slash128v6/DC34_Cnet_Badge/images/IMG_5186.JPEG

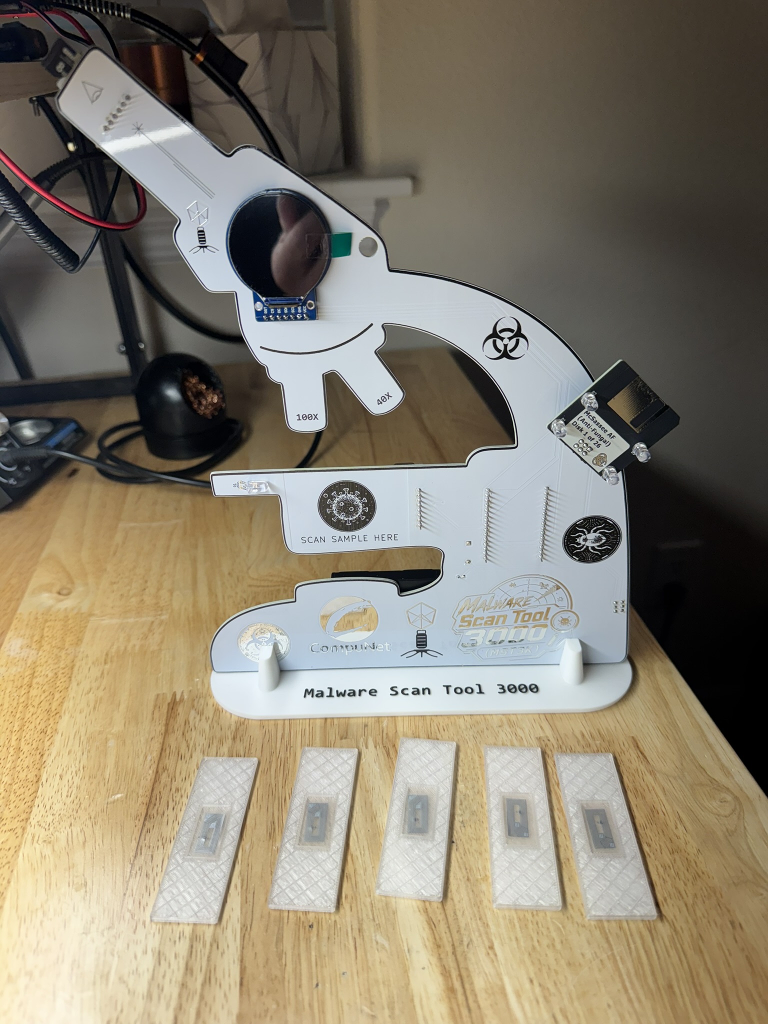
images/IMG_5186.JPEG
