slash128v6/DC34_Cnet_Badge/images/Screenshot 2026-06-05 122044.png

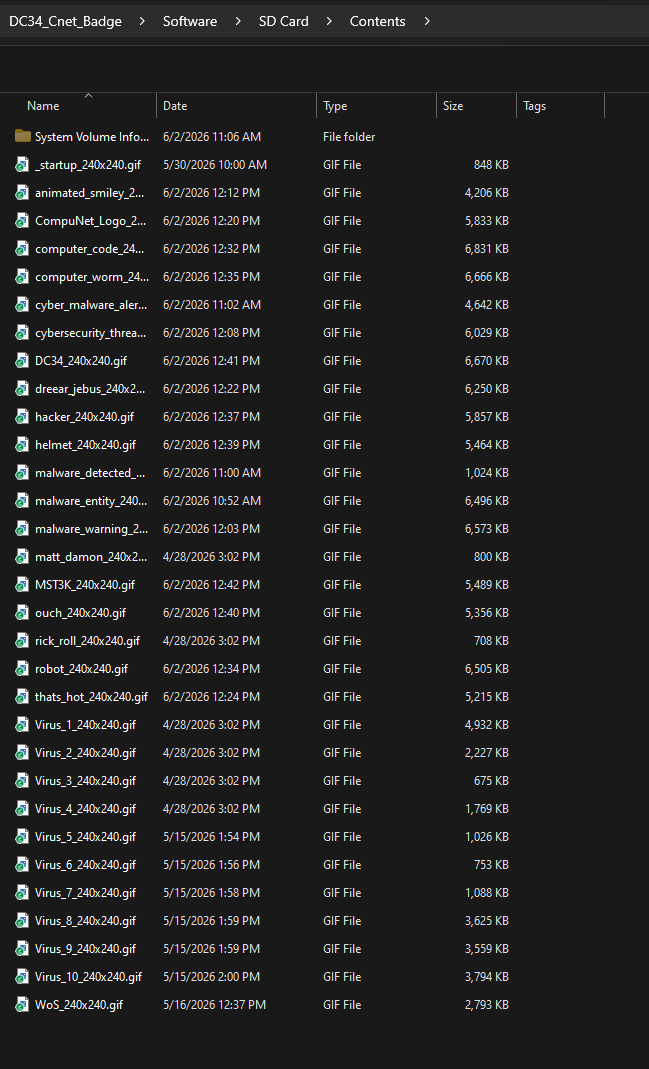
images/Screenshot 2026-06-05 122044.png
