slash128v6/DC34_Cnet_Badge/Join CompuNet & Critical Start at Defcon!.jpg

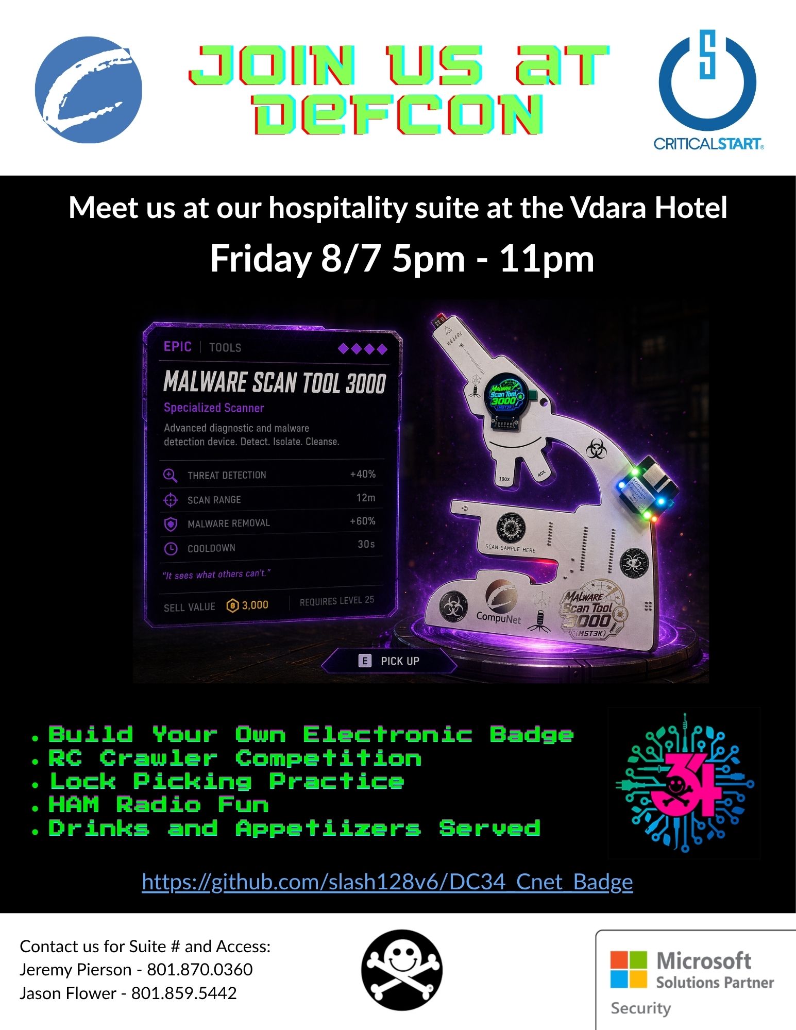
Join CompuNet & Critical Start at Defcon!.jpg
