slash128v6/DC34_Cnet_Badge/Software/SD Card/Contents/_startup_240x240.gif

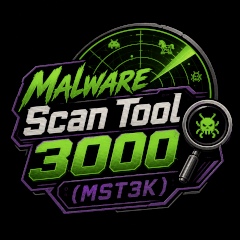
Software/SD Card/Contents/_startup_240x240.gif
